dibaltic/koeleria/gallery/CaseBottom.jpg

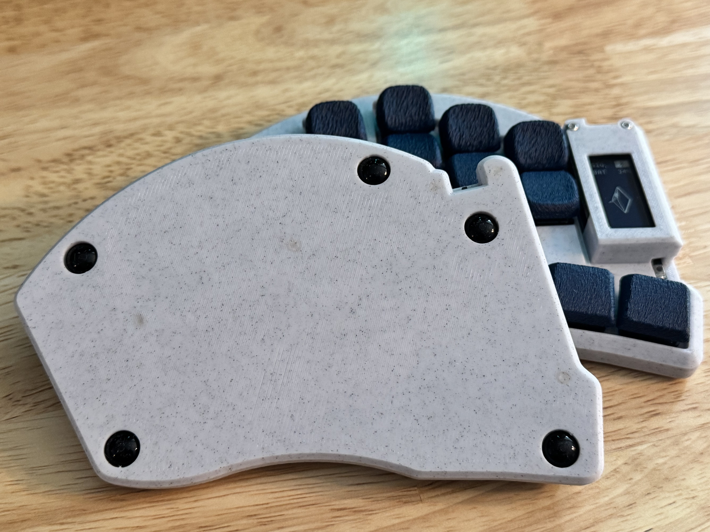
gallery/CaseBottom.jpg
