dibaltic/koeleria/gallery/MinimalAndEnclosed.jpg

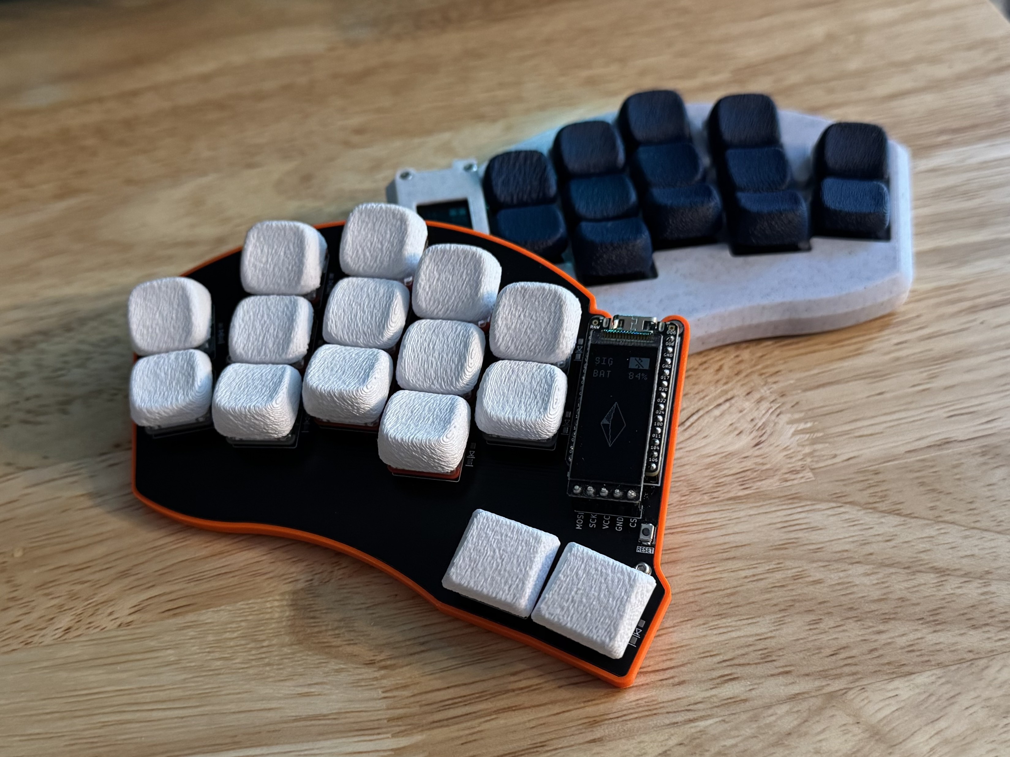
gallery/MinimalAndEnclosed.jpg
