dibaltic/koeleria/gallery/MinimalTop.jpg

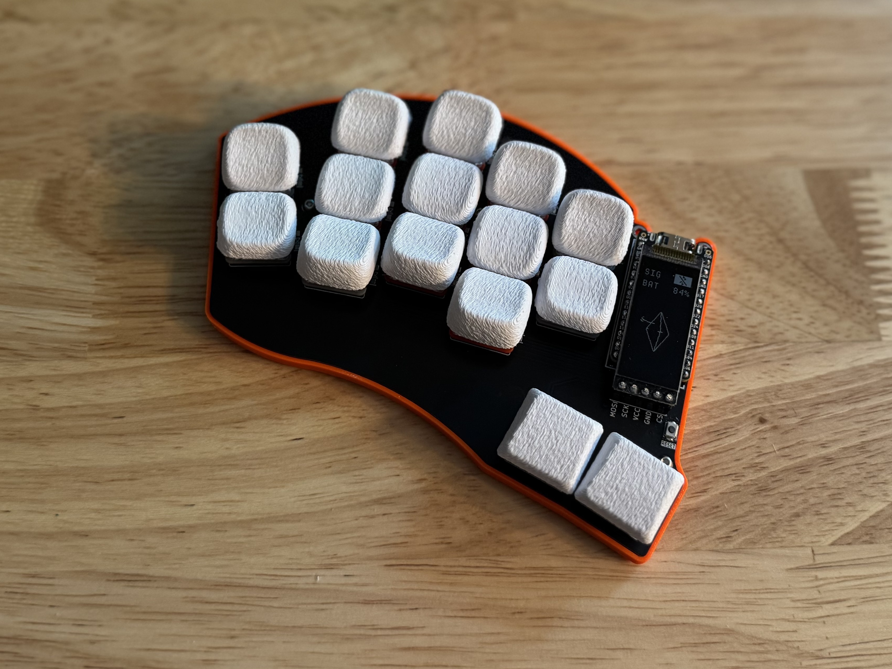
gallery/MinimalTop.jpg
