dibaltic/koeleria/gallery/SideProfile.jpg

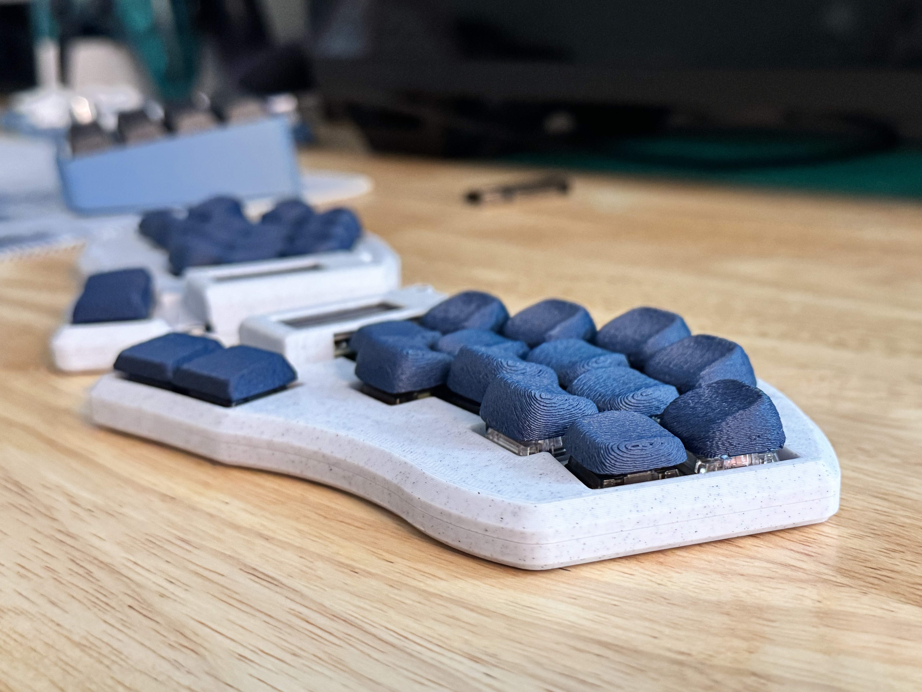
gallery/SideProfile.jpg
