dibaltic/koeleria/gallery/StorageCase2.jpg

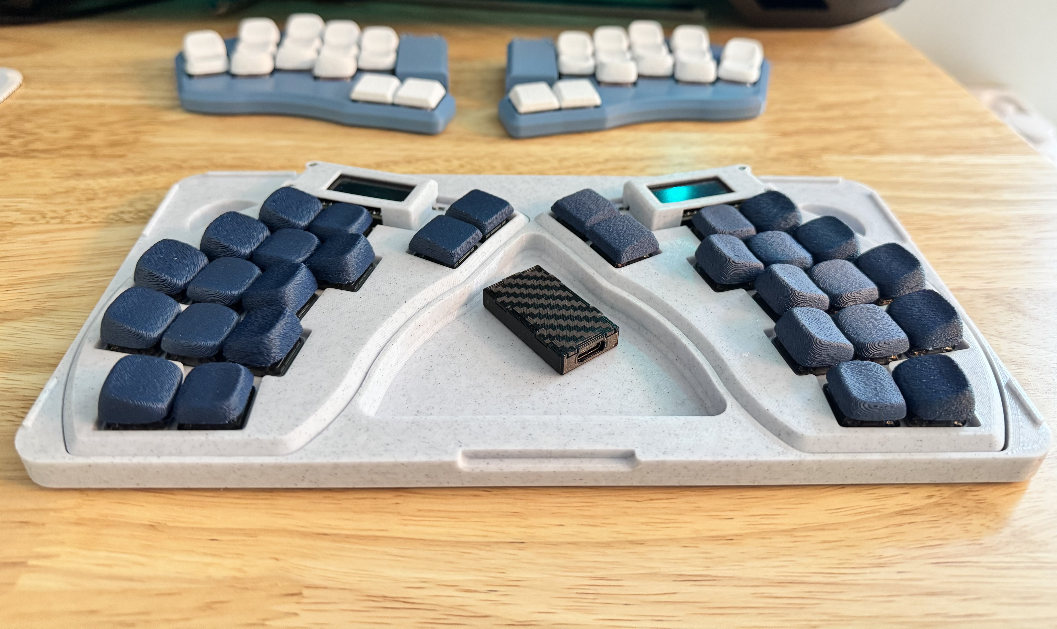
gallery/StorageCase2.jpg
