dibaltic/koeleria/gallery/StorageCase3.jpg

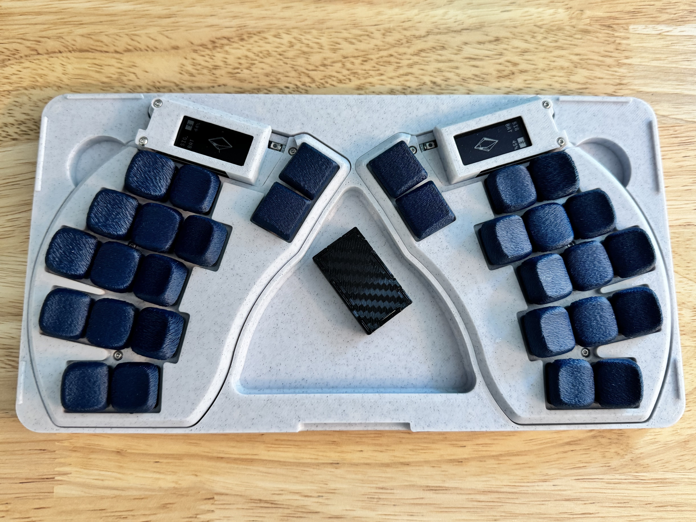
gallery/StorageCase3.jpg
