dibaltic/koeleria/gallery/TentingSide.jpg

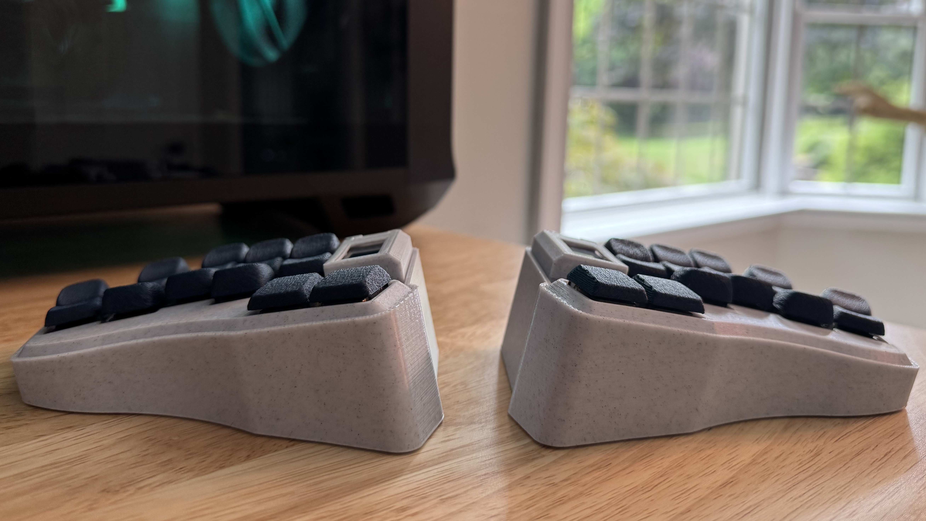
gallery/TentingSide.jpg
