dibaltic/koeleria/gallery/TentingTop.jpg

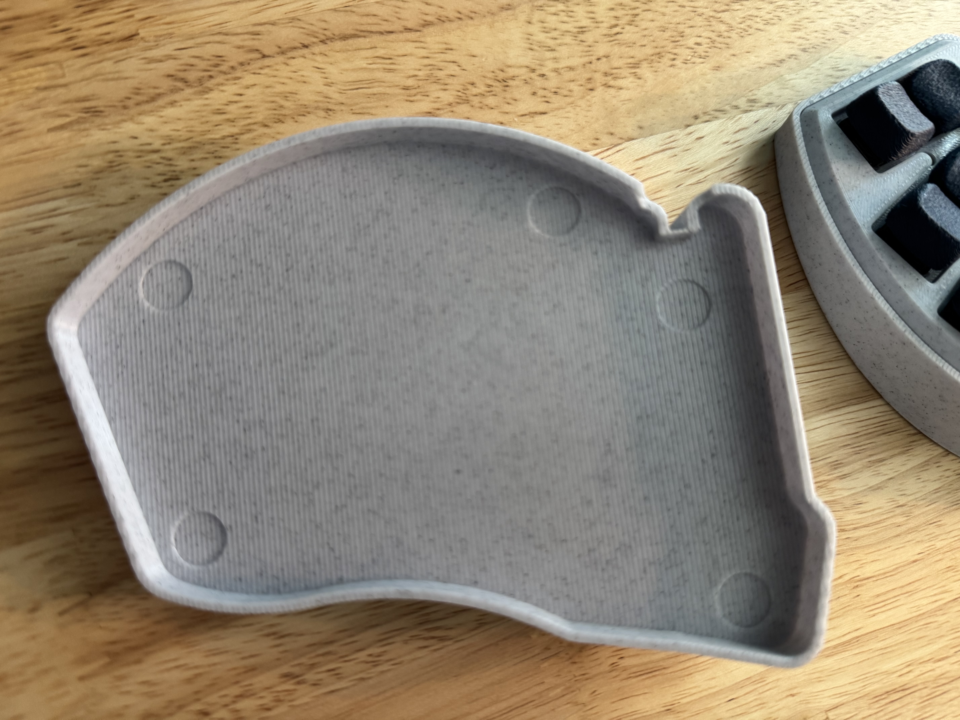
gallery/TentingTop.jpg
