dibaltic/koeleria/gallery/Unibody.jpg

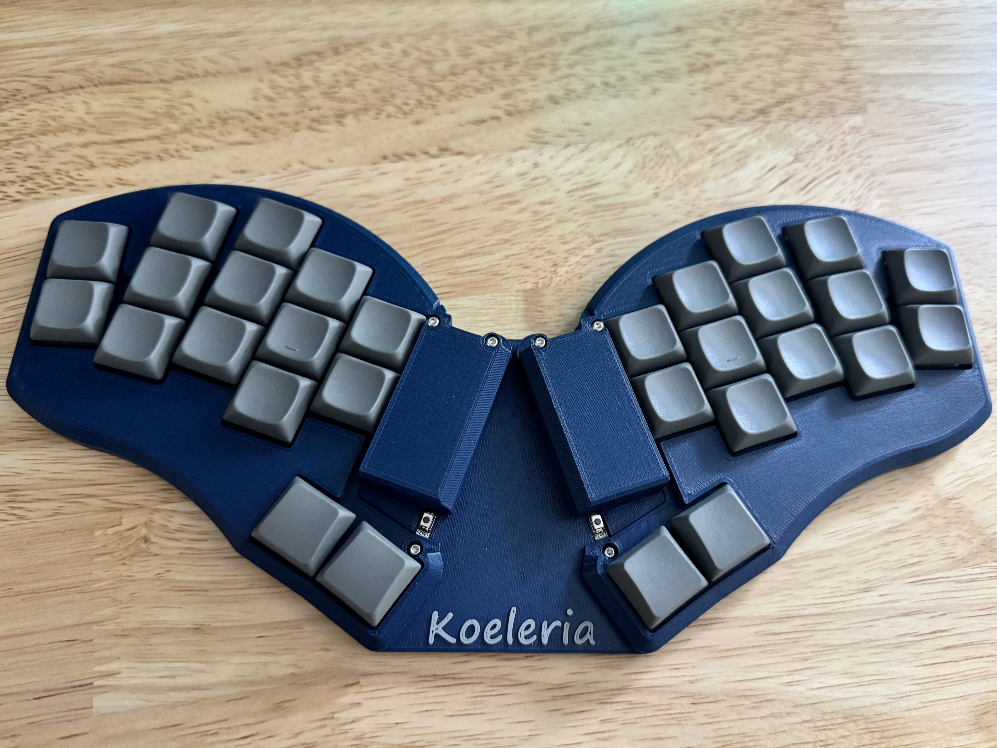
gallery/Unibody.jpg
