dibaltic/koeleria/gallery/UnibodyAndSplit.jpg

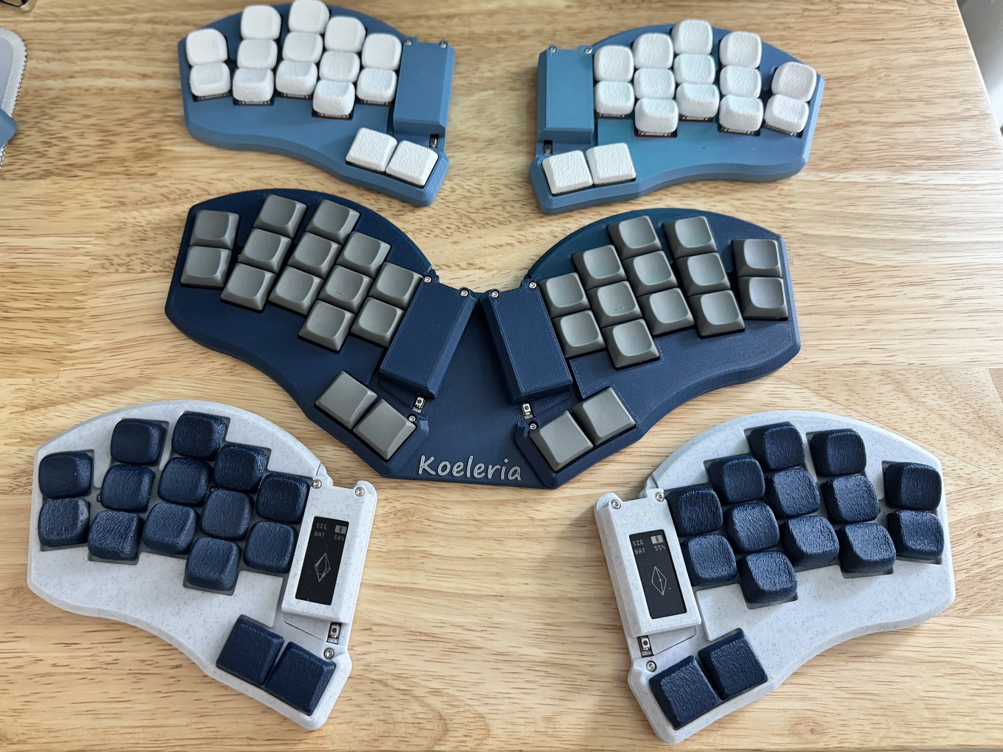
gallery/UnibodyAndSplit.jpg
