dibaltic/koeleria/3d_Print/Tenting/Step/tenting12degreeLeft.step

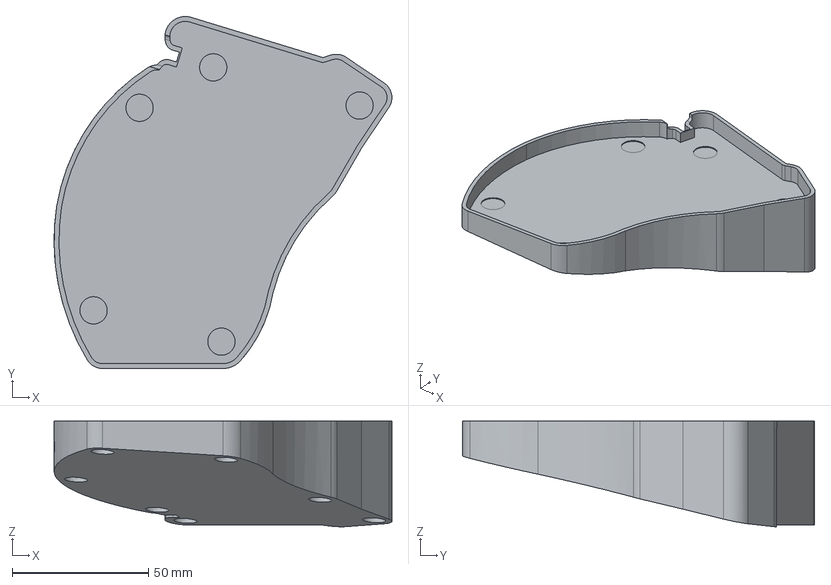
[picture p26: CAD file, 2025-07-12]
3d_Print/Tenting/Step/tenting12degreeLeft.step
123.8 x 128.9 x 38.7 mm
