dibaltic/koeleria/3d_Print/Unibody/Print/UnibodyName.stl

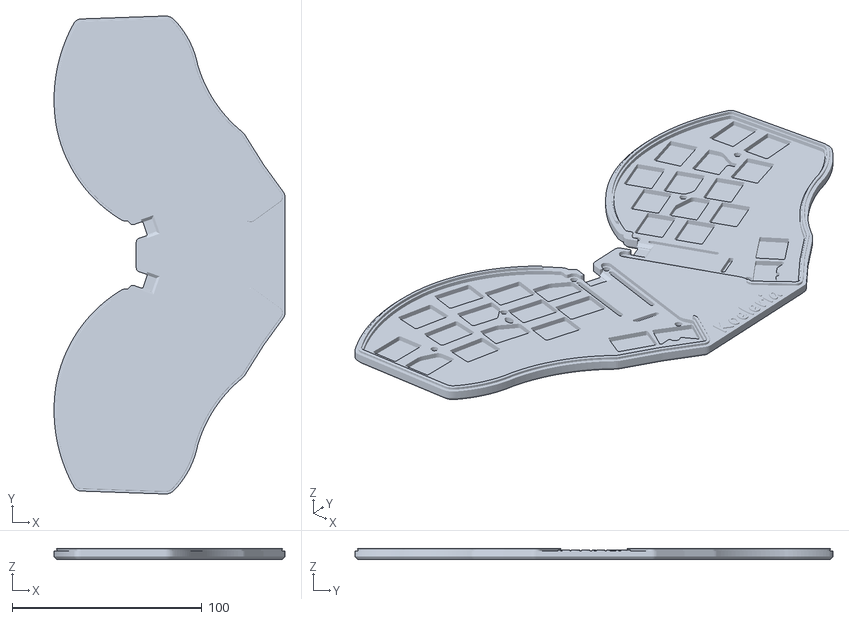
[picture p27: CAD file, 2025-07-12]
3d_Print/Unibody/Print/UnibodyName.stl
121.6 x 251.6 x 5.85
