dibaltic/koeleria/3d_Print/CaseSplitEnclosed/Step/LeftBottom.step

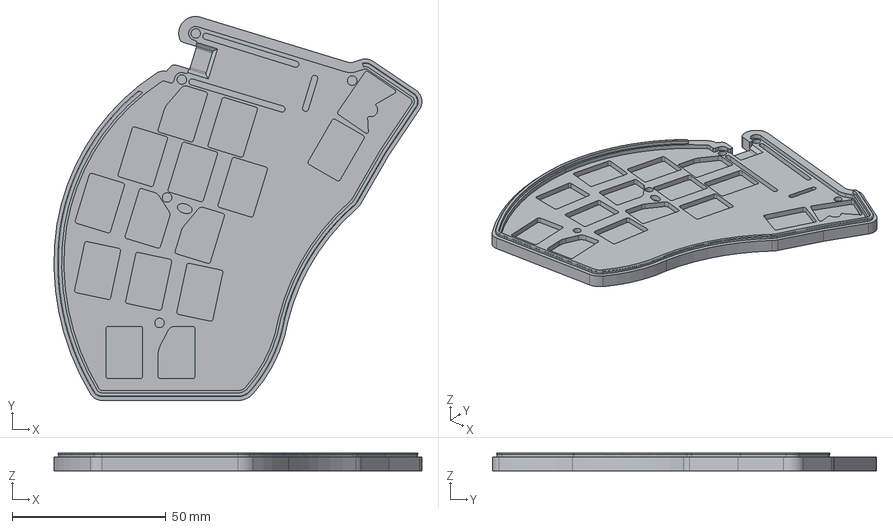
[picture p28: CAD file, 2025-07-12]
3d_Print/CaseSplitEnclosed/Step/LeftBottom.step
119.7 x 124.9 x 5.85 mm
