dibaltic/koeleria/3d_Print/Tenting/Step/tenting7degreeLeft.step

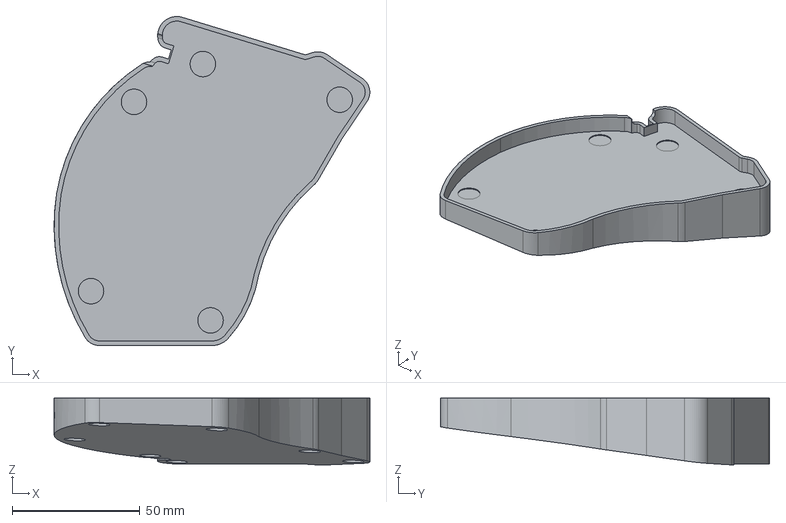
[picture p29: CAD file, 2025-07-12]
3d_Print/Tenting/Step/tenting7degreeLeft.step
123.8 x 129.0 x 26.3 mm
