dibaltic/koeleria/3d_Print/Unibody/Print/RightMcuCoverChamfer.stl

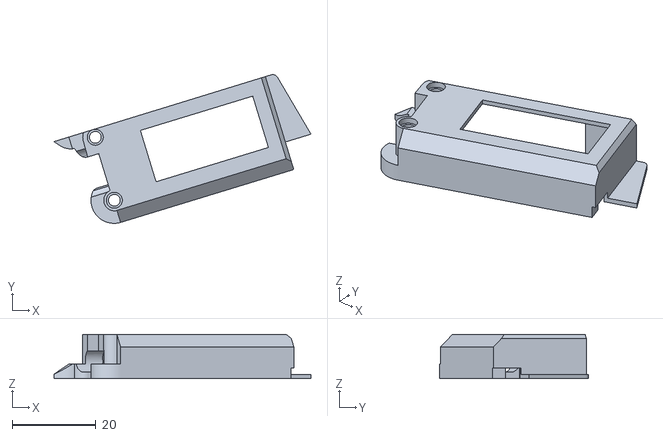
[picture p30: CAD file, 2025-07-12]
3d_Print/Unibody/Print/RightMcuCoverChamfer.stl
61.3 x 35.5 x 10.6
