dibaltic/koeleria/3d_Print/Unibody/Print/RightMcuCoverNoDispChamfer.stl

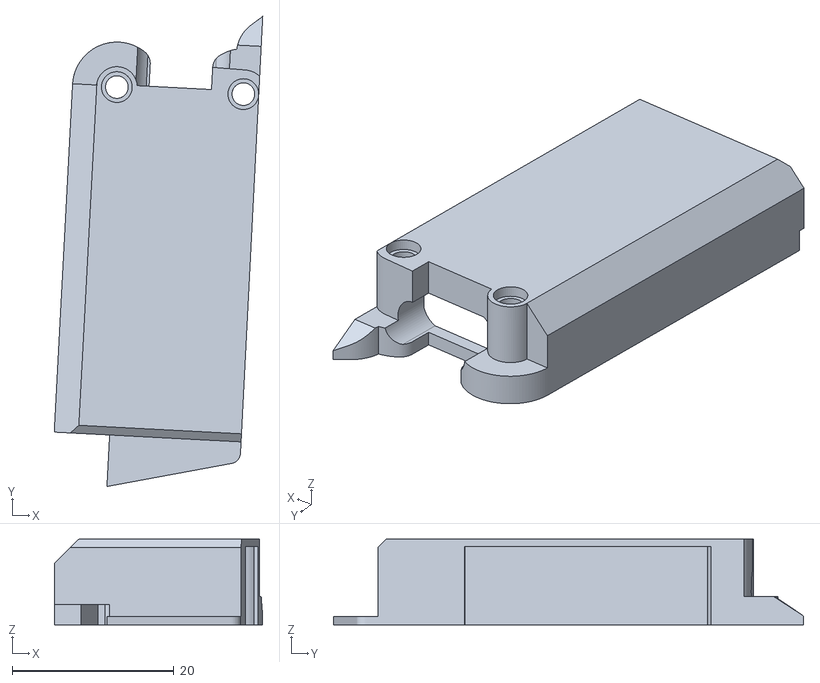
[picture p31: CAD file, 2025-07-12]
3d_Print/Unibody/Print/RightMcuCoverNoDispChamfer.stl
25.8 x 58.2 x 10.6
