dibaltic/koeleria/3d_Print/Unibody/Print/LeftMcuCoverNoDispChamfer.stl

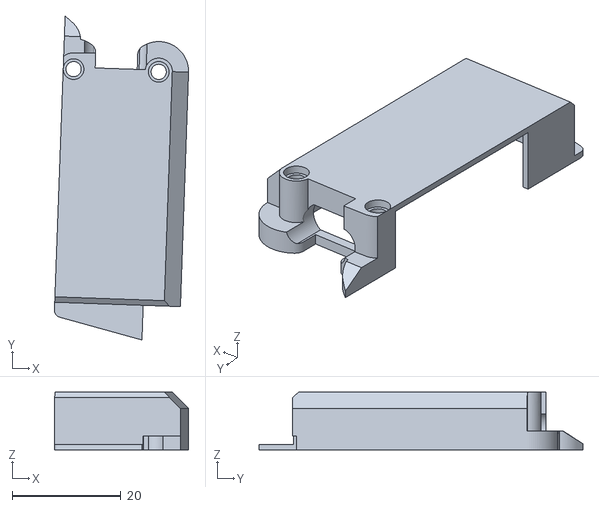
[picture p32: CAD file, 2025-07-12]
3d_Print/Unibody/Print/LeftMcuCoverNoDispChamfer.stl
24.7 x 59.6 x 10.6
